EGR314-Team-305/GroupProjectWebsite/media/Framework 1.jpg

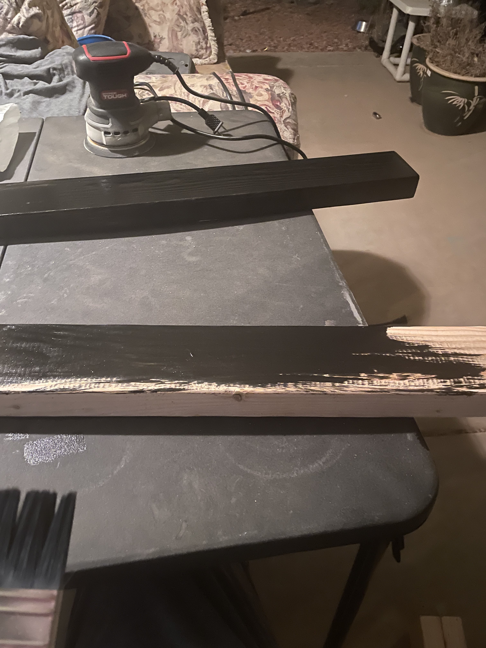
media/Framework 1.jpg
